nauti-control/STWirelessRemote/img/IMG_20231207_133401_511.jpg

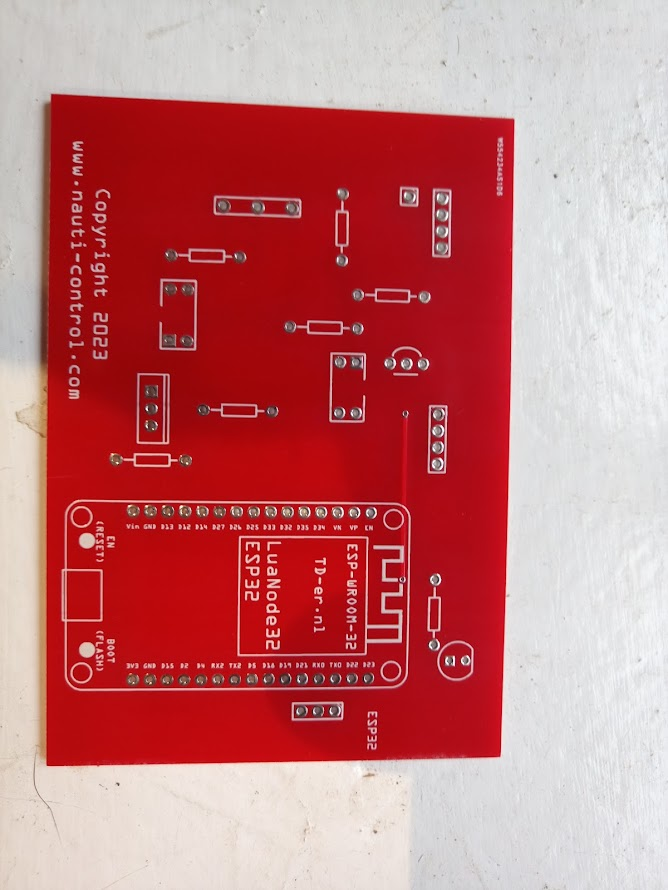
img/IMG_20231207_133401_511.jpg
