nauti-control/STWirelessRemote/img/IMG_20231215_121948_274.jpg

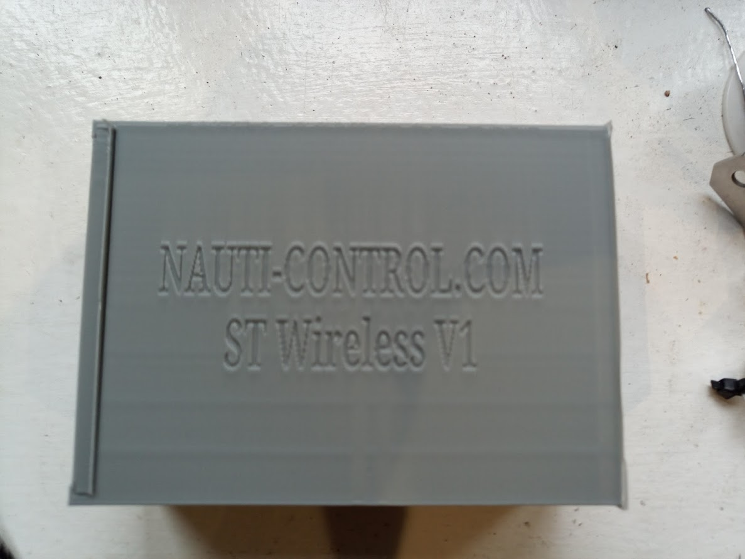
img/IMG_20231215_121948_274.jpg
