nauti-control/STWirelessRemote/img/IMG_20231215_122422_546.jpg

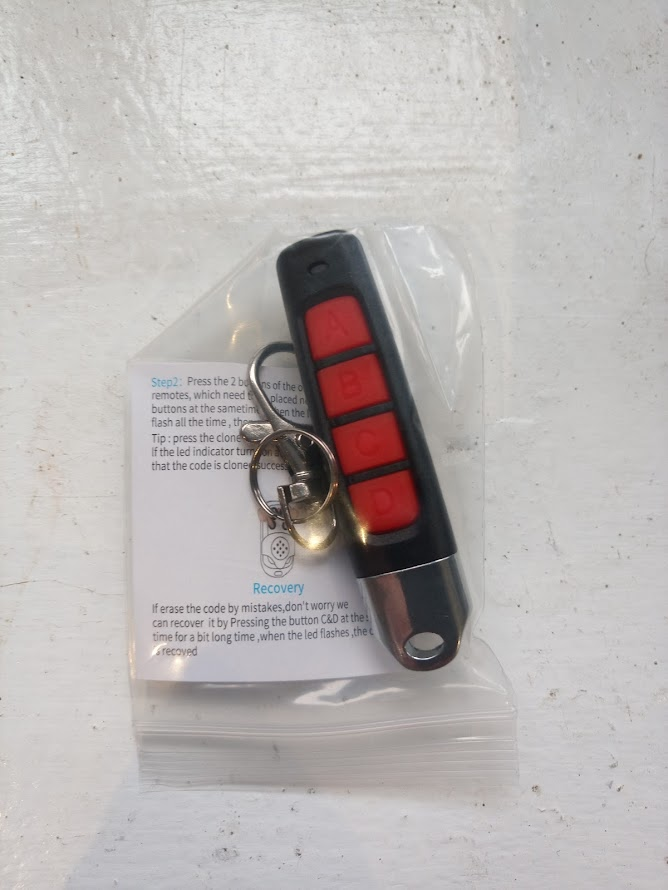
img/IMG_20231215_122422_546.jpg
